o7-machinehum/phantomdrive/src/phantomdrive.h

#ifndef PHANTOMDRIVE_H_
#define PHANTOMDRIVE_H_

#include <stdint.h>
#include <stddef.h>
#include <stdbool.h>

#define STATE_LOCKED    0
#define STATE_UNLOCKED  1
#ifndef LOCKED_SECTORS
#define LOCKED_SECTORS  (16777216UL)  /* 8 GiB in sectors */
#endif

void phantomdrive_init(uint64_t unique_id);
void phantomdrive_snoop_write(uint8_t *buf, uint32_t len);
bool phantomdrive_get_unlock_pending(void);
void phantomdrive_unlock(void);
bool phantomdrive_is_locked(void);
void phantomdrive_encrypt_buf(uint8_t *buf, uint32_t sd_lba, uint16_t num_sectors);
void phantomdrive_decrypt_buf(uint8_t *buf, uint32_t sd_lba, uint16_t num_sectors);
void phantomdrive_ecdc_disable_data_path(void);

#endif /* PHANTOMDRIVE_H_ */
