o7-machinehum/phantomdrive/src/sw_udisk.h

/* sw_udisk.h - USB ISR bridge to the MSC BOT handlers
 *
 * The WCH USB ISR files include this project header for BOT state and
 * endpoint callbacks.
 *
 * SPDX-License-Identifier: Apache-2.0
 */
#ifndef SW_UDISK_H_
#define SW_UDISK_H_

#include "bot_state.h"
#include "bot.h"

#endif /* SW_UDISK_H_ */
